Heber-co-uk/Multisystem/images/Expansion_connections_layout.jpg

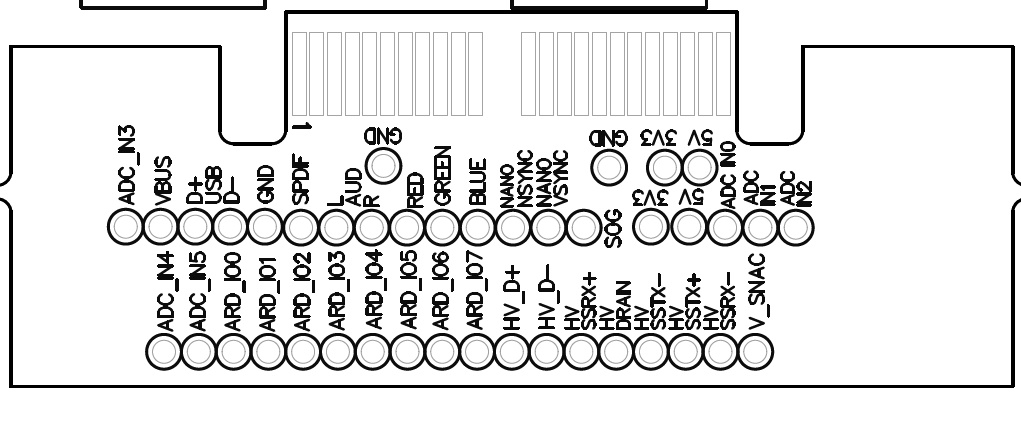
images/Expansion_connections_layout.jpg
