Heber-co-uk/Multisystem/images/MMS_2022_Black_grey_white.jpg

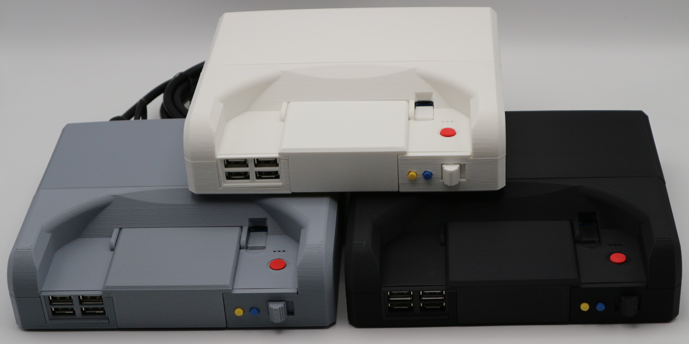
images/MMS_2022_Black_grey_white.jpg
