Heber-co-uk/Multisystem/images/MMS_PSX_enclosure_with_MMS_V6.jpg

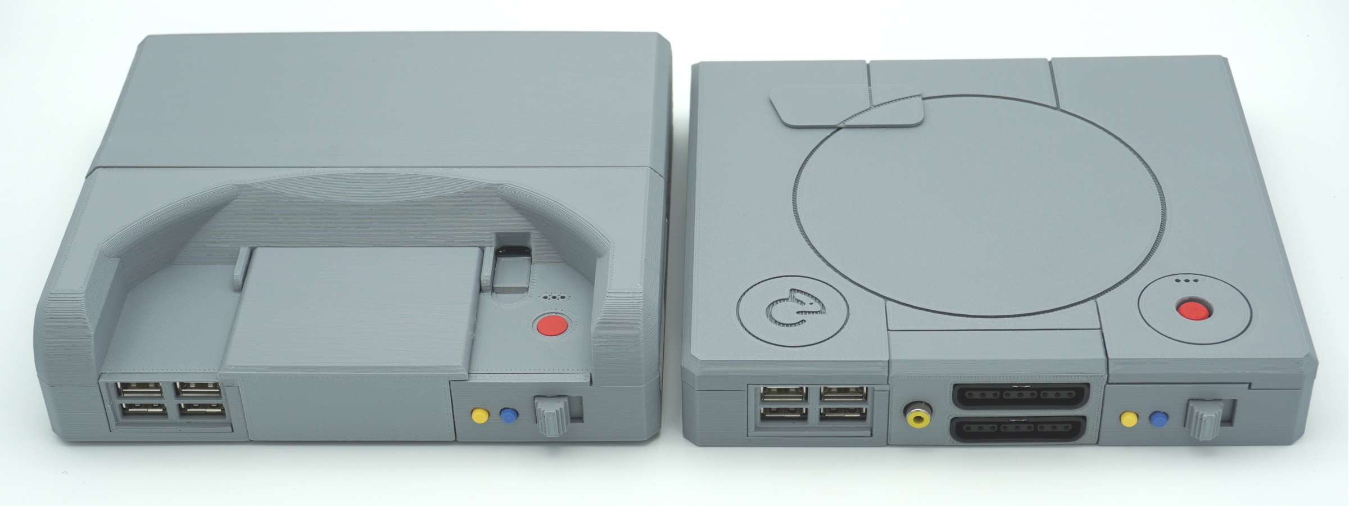
images/MMS_PSX_enclosure_with_MMS_V6.jpg
