Heber-co-uk/Multisystem/images/MMS_PSX_enclosure_with_ports.jpg

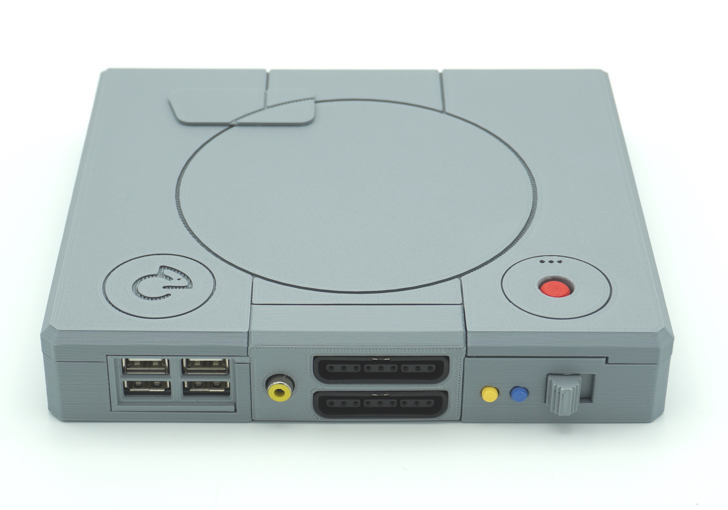
images/MMS_PSX_enclosure_with_ports.jpg
