Heber-co-uk/Multisystem/images/Multisystem_Cables_fitted.jpg

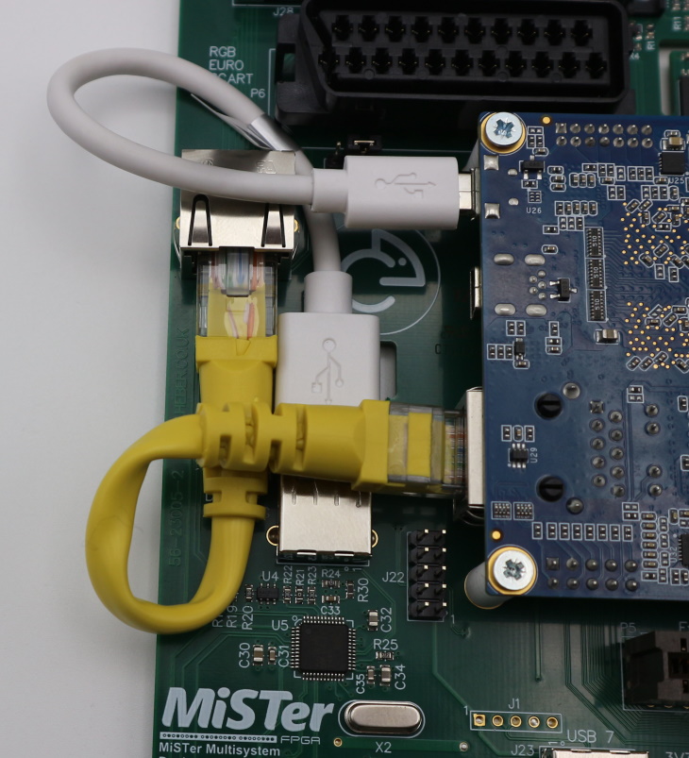
images/Multisystem_Cables_fitted.jpg
