Heber-co-uk/Multisystem/images/Multisystem_Case_checking_user_buttons_fitted.jpg

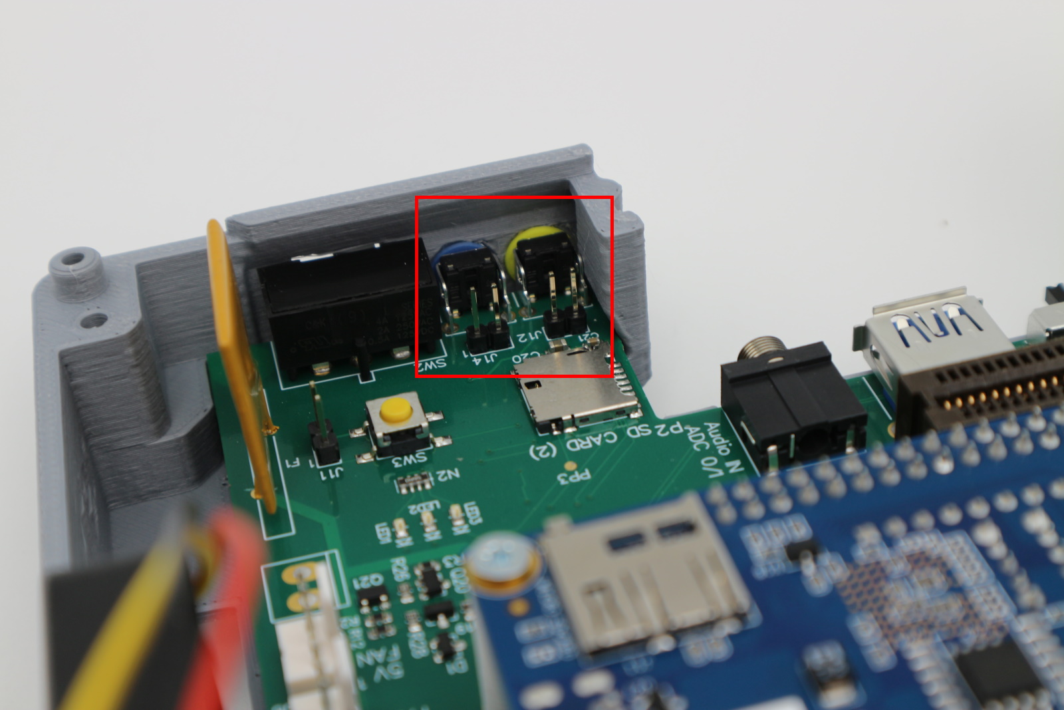
images/Multisystem_Case_checking_user_buttons_fitted.jpg
