Heber-co-uk/Multisystem/images/Multisystem_Case_fitting_board_into_base.jpg

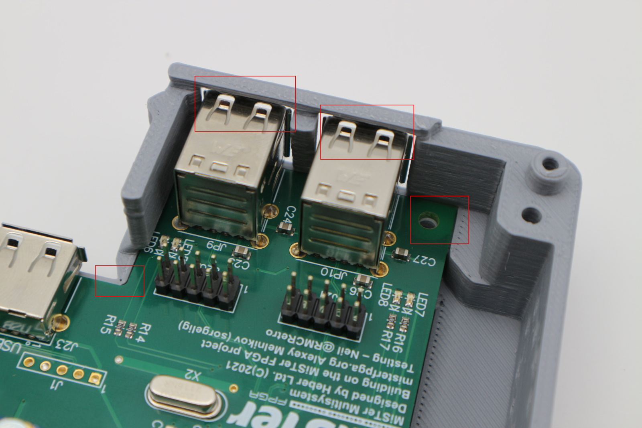
images/Multisystem_Case_fitting_board_into_base.jpg
