Heber-co-uk/Multisystem/images/Multisystem_EXPANSION.jpg

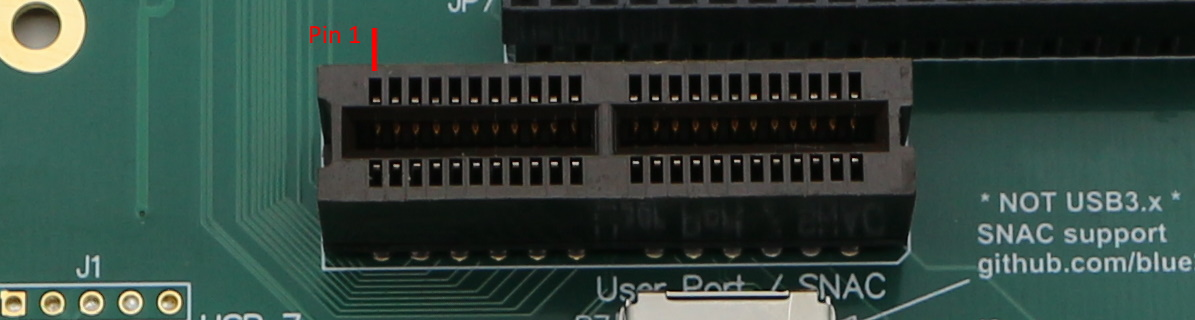
images/Multisystem_EXPANSION.jpg
