Heber-co-uk/Multisystem/images/Multisystem_FRONT_SWITCHES.jpg

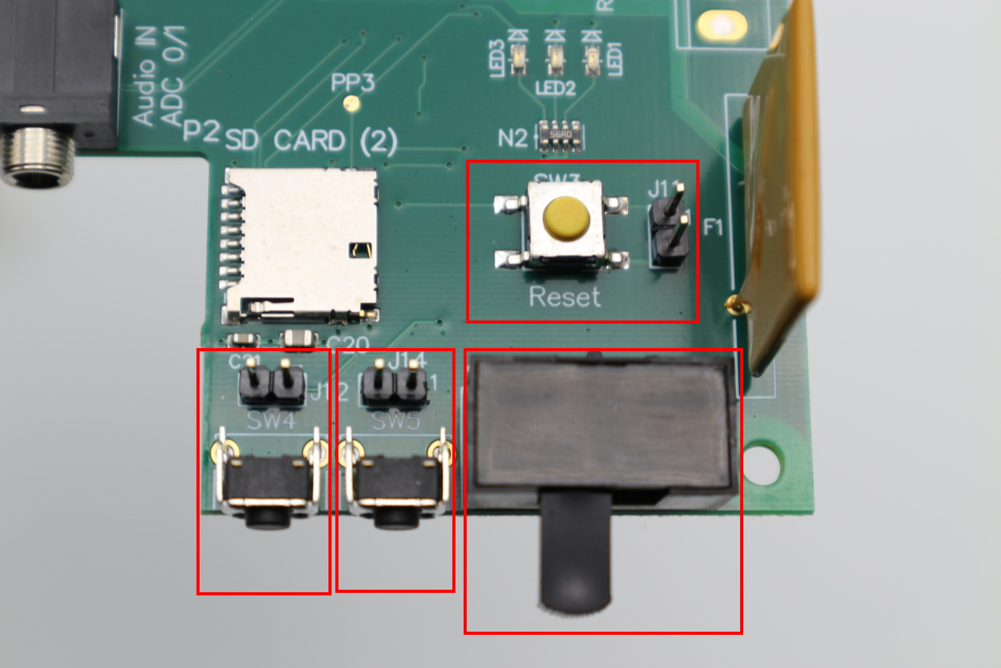
images/Multisystem_FRONT_SWITCHES.jpg
