Heber-co-uk/Multisystem/images/Multisystem_HDMI_BRIDGE_BOARD.jpg

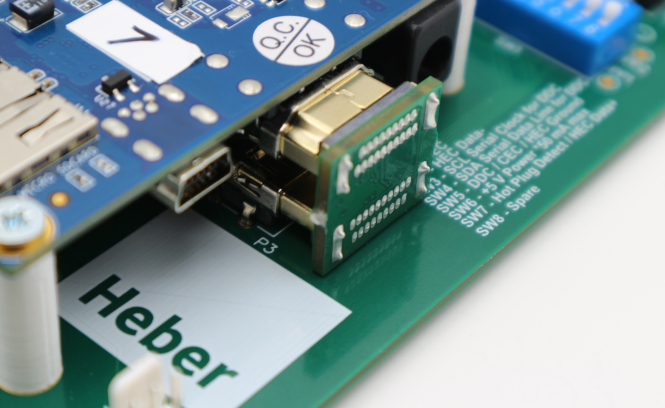
images/Multisystem_HDMI_BRIDGE_BOARD.jpg
