Heber-co-uk/Multisystem/images/Multisystem_MarkUP_With_Text.jpg

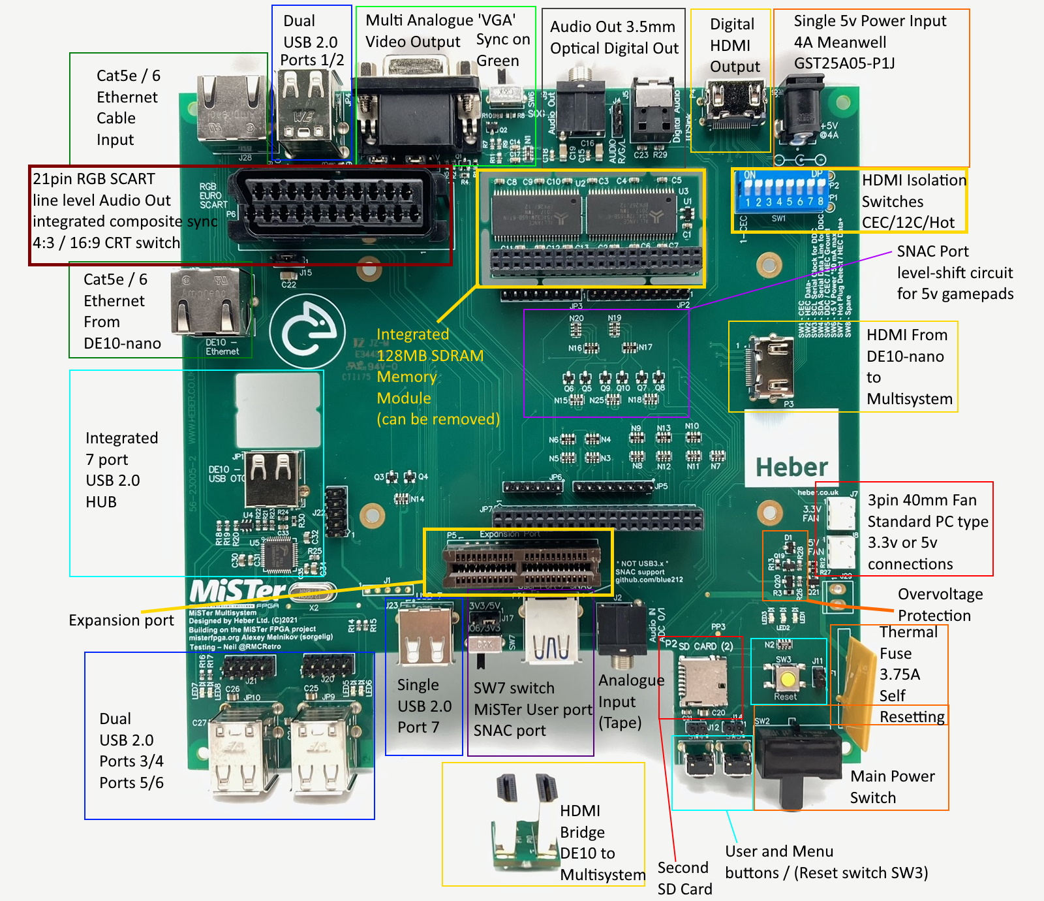
images/Multisystem_MarkUP_With_Text.jpg
