Heber-co-uk/Multisystem/images/Multisystem_PCB_as_delivered.jpg

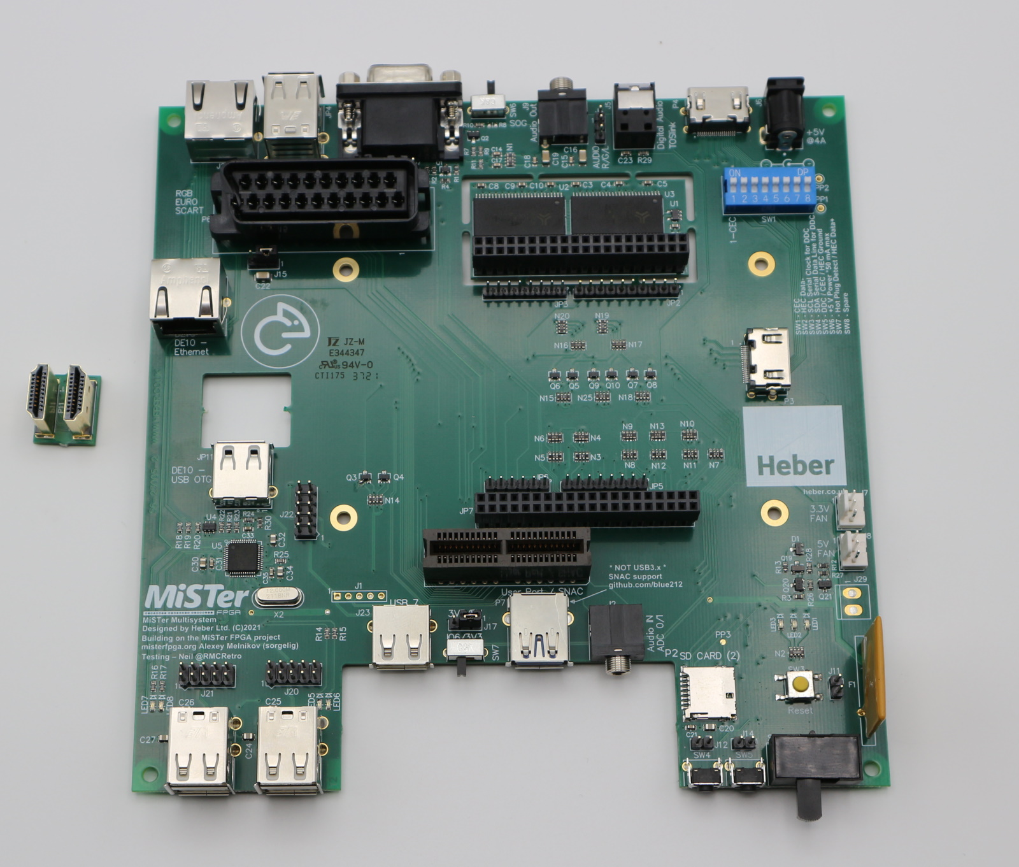
images/Multisystem_PCB_as_delivered.jpg
