Heber-co-uk/Multisystem/images/Multisystem_PCB_standard_front_jumper_switch_positions.jpg

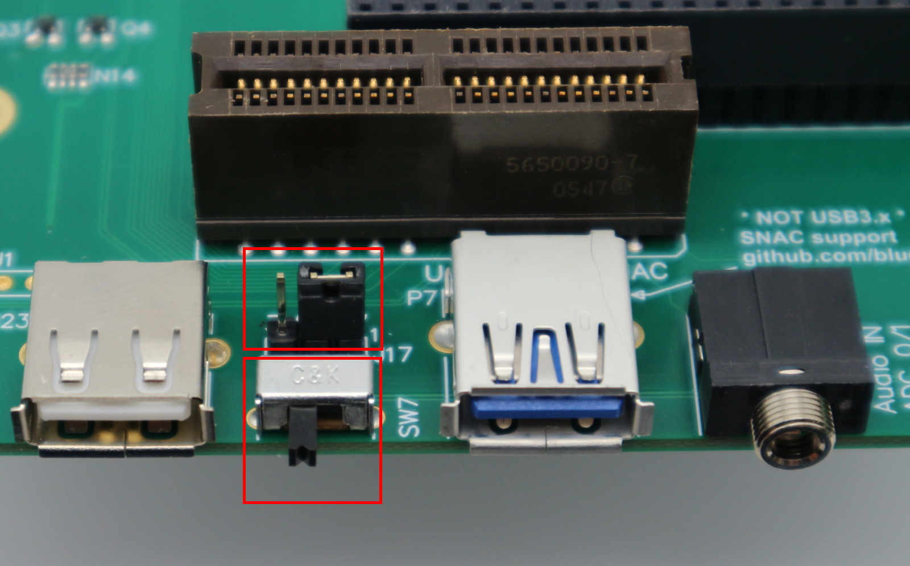
images/Multisystem_PCB_standard_front_jumper_switch_positions.jpg
