Heber-co-uk/Multisystem/images/Multisystem_PCB_standard_SCART_jumper_position.jpg

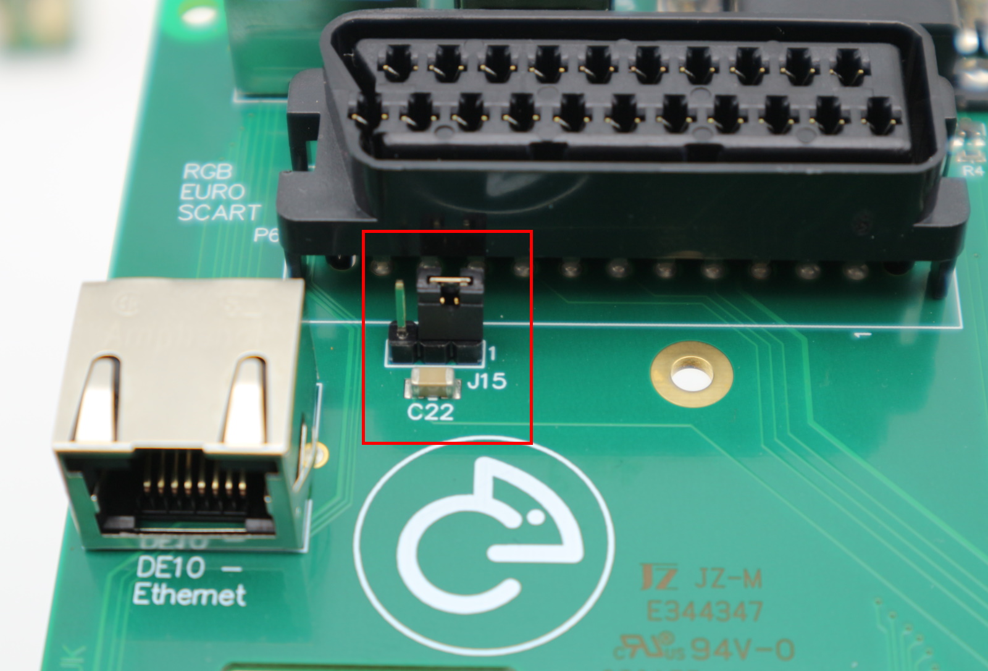
images/Multisystem_PCB_standard_SCART_jumper_position.jpg
