Heber-co-uk/Multisystem/images/Multisystem_SNAC_Gameboy_link.jpg

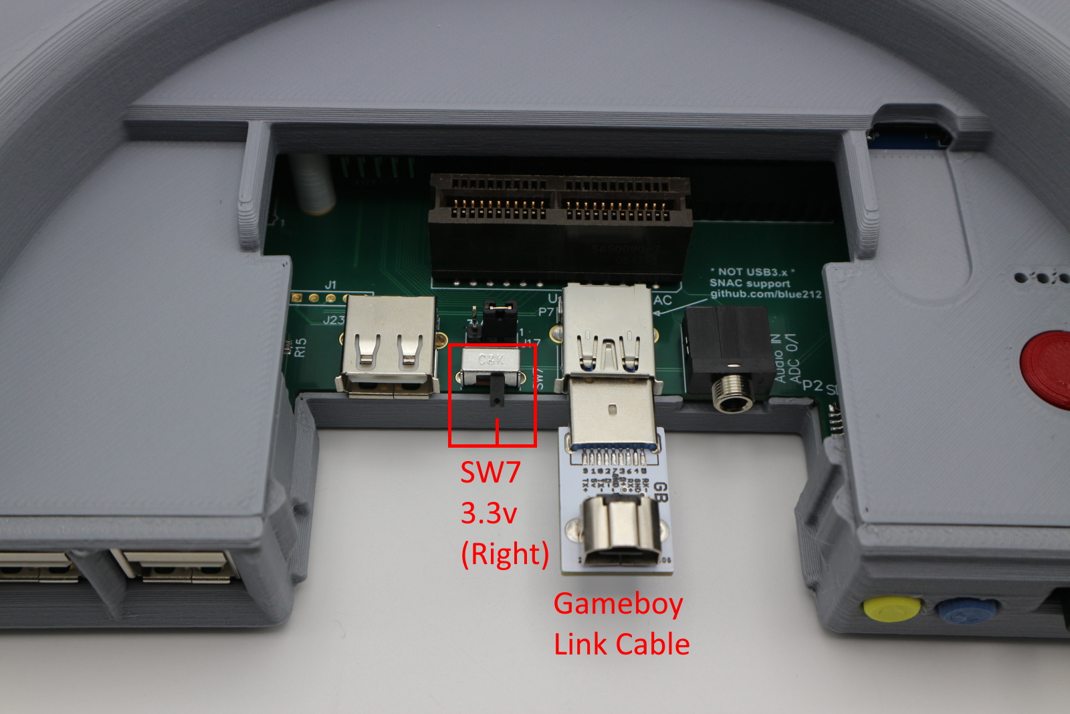
images/Multisystem_SNAC_Gameboy_link.jpg
