Heber-co-uk/Multisystem/images/Multisystem_SNAC_MD.jpg

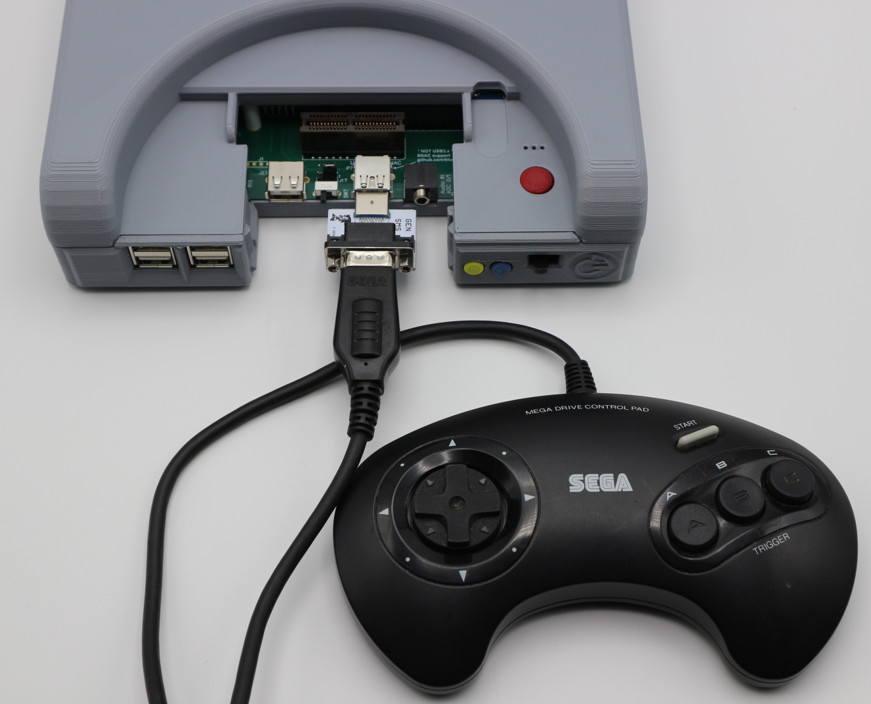
images/Multisystem_SNAC_MD.jpg
