Heber-co-uk/Multisystem/images/Multisystem_USB_conections.jpg

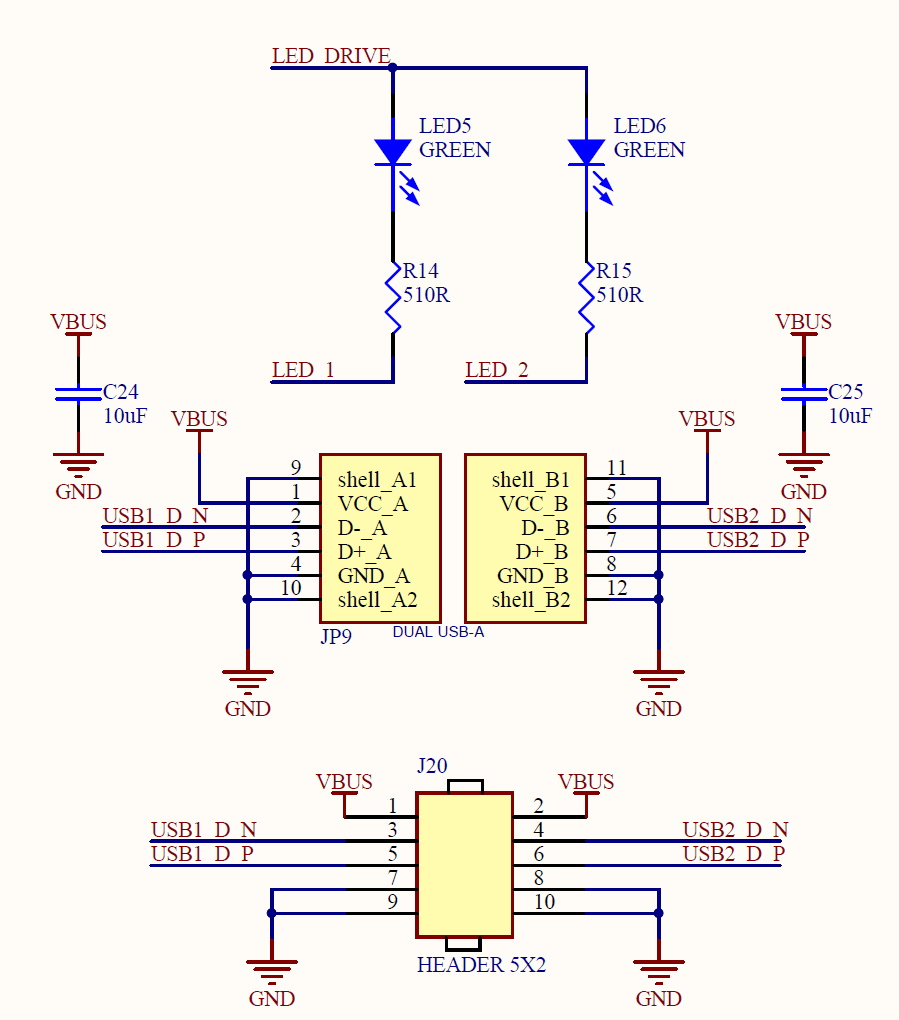
images/Multisystem_USB_conections.jpg
