Heber-co-uk/Multisystem/images/Multisystem_V5_Muted_FULL_SIZE.jpg

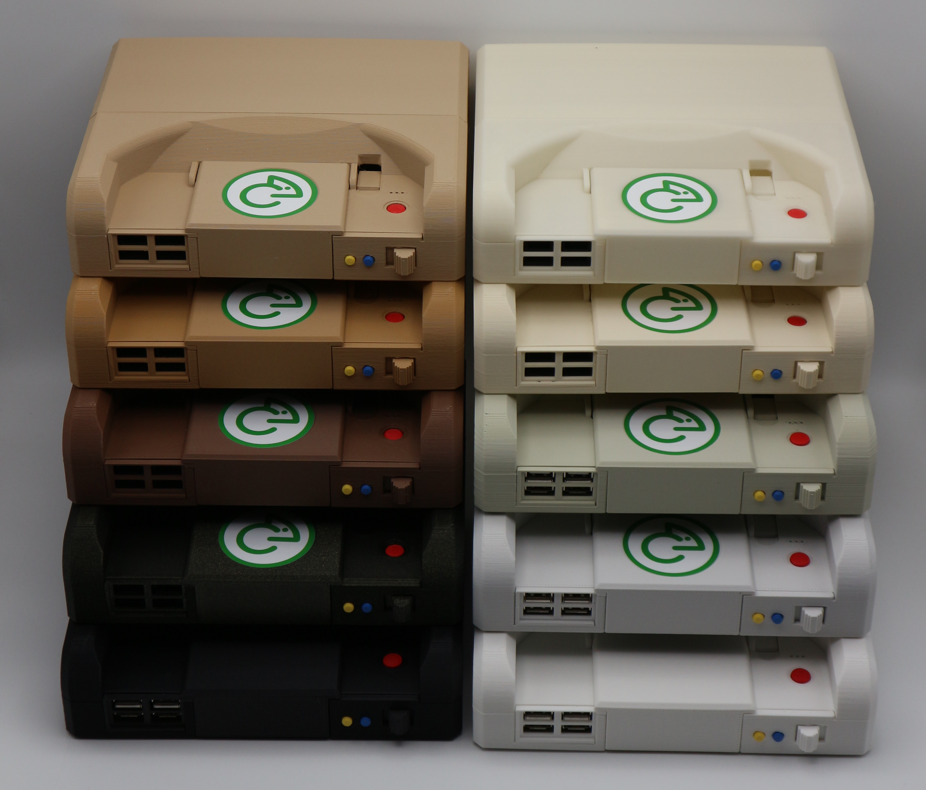
images/Multisystem_V5_Muted_FULL_SIZE.jpg
