Heber-co-uk/Multisystem/images/PiMMS_Fitted_in_white_case_ISO.jpg

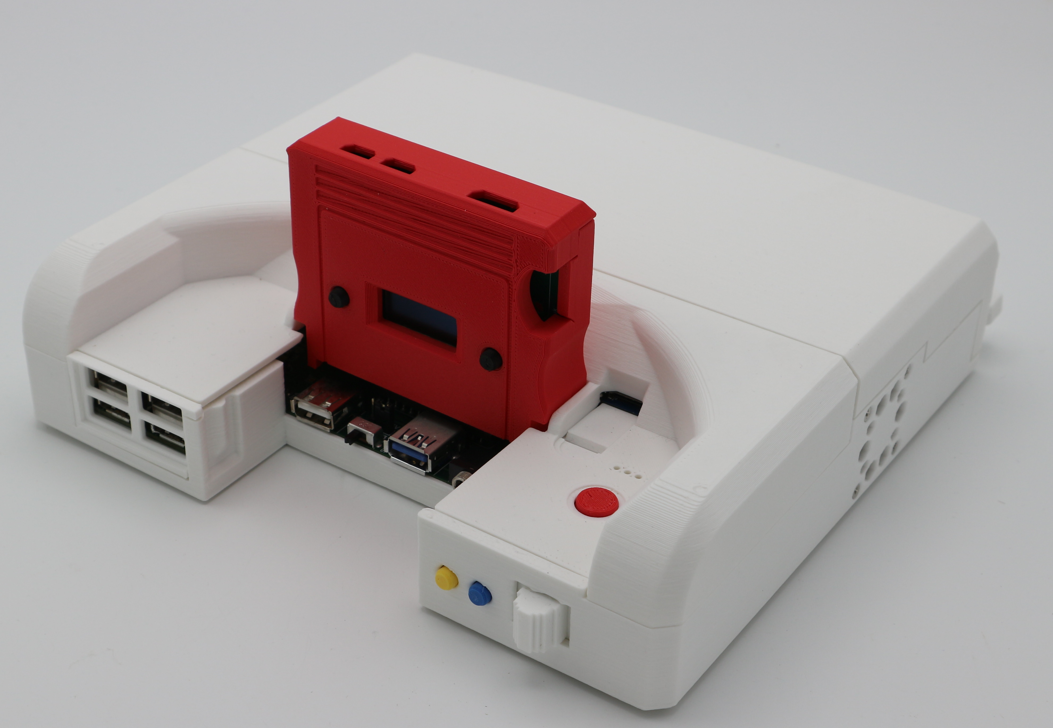
images/PiMMS_Fitted_in_white_case_ISO.jpg
