Heber-co-uk/Multisystem/images/Super_CTRLDock_and_NES_Advantage.jpg

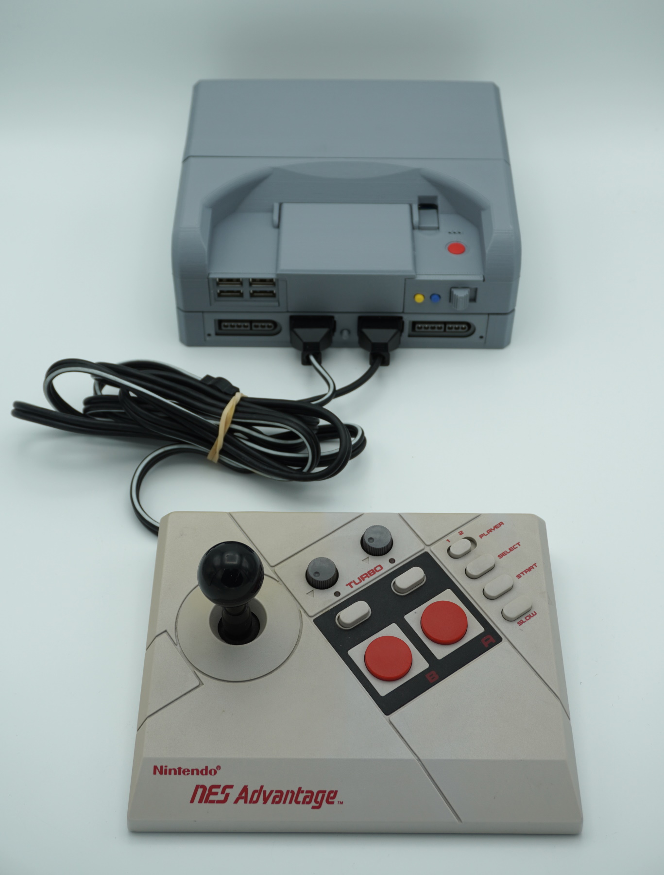
images/Super_CTRLDock_and_NES_Advantage.jpg
