Heber-co-uk/Multisystem/images/MMS_with_SVIDEO_fitted_back_ports_small_for_manual.jpg

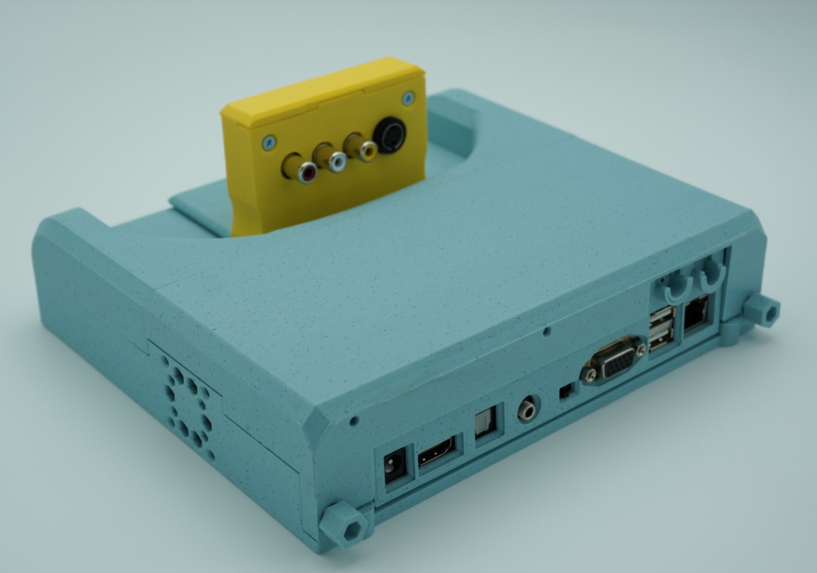
images/MMS_with_SVIDEO_fitted_back_ports_small_for_manual.jpg
