Heber-co-uk/Multisystem/images/Multisystem_DE10_posts_installed_on_top.jpg

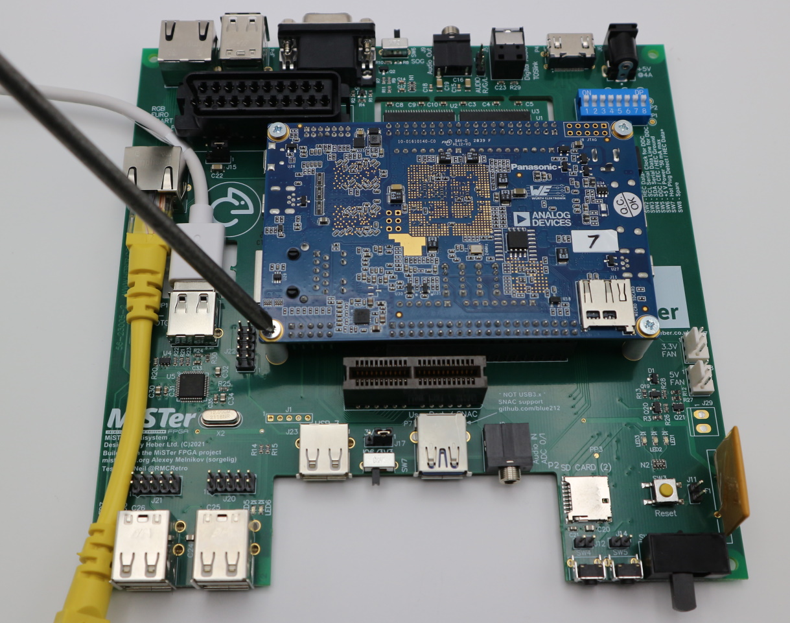
images/Multisystem_DE10_posts_installed_on_top.jpg
